ohdsp/uCODEC/Drawings/PCB Layers/PDF/uCODEC-1.0-F_SilkS.pdf

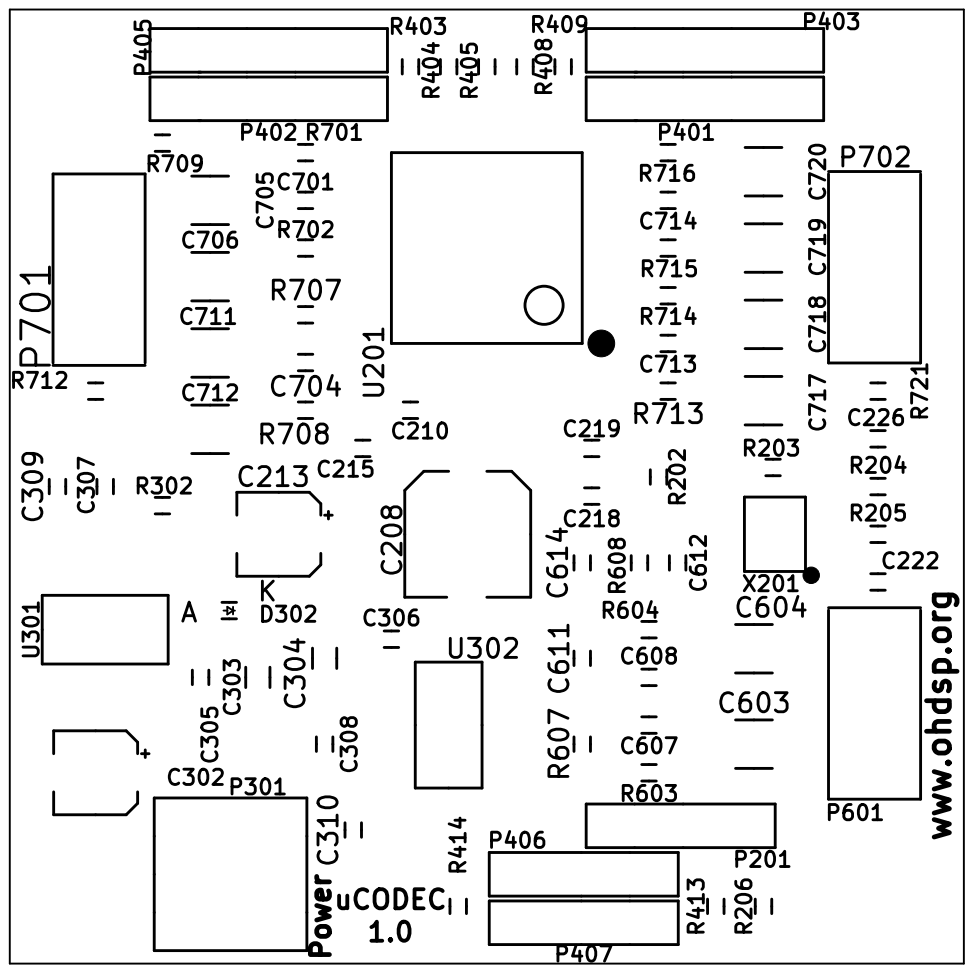
[picture p12: page 1]

Copyright Paul Janicki 2019 www.ohdsp.org Power uCODEC

Licensed under the TAPR Open Hardware License (www.tapr.org/OHL). This documentation
is distributed WITHOUT ANY EXPRESS OR IMPLIED WARRANTY, INCLUDING OF
MERCHANTABILITY, SATISFACTORY QUALITY AND FITNESS FOR A PARTICULAR PURPOSE.
File: uCODEC-1.0.kicad_pcb Sheet: Open Hardware DSP Platform - www.ohdsp.org
